kallikak/Euclidean/Euclid/sawtoothWave.h

const int16_t sawtoothWavetable[45][257] = {{-0,28031,27765,27259,27213,27036,26679,26531,26359,26050,25863,25691,25407,25200,25026,24759,24540,24363,24109,23881,23700,23457,23222,23038,22803,22565,22376,22149,21908,21714,21494,21252,21053,20838,20596,20392,20181,19940,19732,19524,19284,19072,18866,18629,18412,18208,17973,17753,17549,17318,17094,16890,16662,16435,16231,16006,15777,15572,15350,15120,14913,14694,14462,14254,14037,13805,13594,13380,13148,12935,12723,12492,12276,12065,11835,11617,11408,11179,10958,10749,10522,10299,10091,9866,9641,9433,9210,8983,8774,8553,8325,8115,7896,7668,7456,7240,7010,6797,6582,6353,6138,5925,5696,5479,5268,5040,4820,4610,4383,4162,3952,3726,3503,3294,3070,2845,2635,2413,2187,1976,1757,1529,1318,1100,872,659,443,214,-0,-214,-443,-659,-872,-1100,-1318,-1529,-1757,-1976,-2187,-2413,-2635,-2845,-3070,-3294,-3503,-3726,-3952,-4162,-4383,-4610,-4820,-5040,-5268,-5479,-5696,-5925,-6138,-6353,-6583,-6797,-7010,-7240,-7456,-7668,-7896,-8115,-8325,-8553,-8774,-8983,-9210,-9433,-9641,-9866,-10091,-10299,-10522,-10749,-10958,-11179,-11408,-11617,-11835,-12065,-12276,-12492,-12723,-12935,-13148,-13380,-13594,-13805,-14037,-14254,-14462,-14694,-14913,-15120,-15350,-15572,-15777,-16006,-16232,-16435,-16662,-16891,-17094,-17318,-17549,-17753,-17973,-18208,-18412,-18629,-18866,-19072,-19285,-19524,-19732,-19940,-20181,-20392,-20596,-20838,-21053,-21252,-21494,-21714,-21908,-22149,-22376,-22565,-22803,-23038,-23222,-23457,-23700,-23881,-24109,-24363,-24540,-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
};
