kallikak/Euclidean/Euclid/squareWave.h

const int16_t squareWavetable[45][257] = {{0,25902,25868,25602,25755,25802,25674,25732,25783,25701,25723,25773,25716,25718,25765,25726,25716,25759,25733,25716,25753,25738,25716,25748,25742,25718,25743,25745,25720,25739,25747,25722,25735,25748,25725,25732,25748,25728,25729,25748,25730,25727,25746,25733,25726,25745,25736,25725,25743,25739,25724,25741,25741,25725,25738,25743,25726,25736,25744,25727,25733,25745,25729,25731,25745,25731,25729,25745,25733,25727,25744,25736,25726,25743,25738,25725,25741,25741,25724,25739,25743,25725,25736,25745,25726,25733,25746,25727,25731,25748,25729,25727,25748,25732,25725,25748,25735,25722,25747,25739,25719,25745,25743,25718,25742,25748,25716,25738,25753,25716,25733,25759,25716,25726,25765,25719,25716,25773,25723,25701,25783,25732,25674,25802,25755,25602,25868,25902,-2,-25902,-25868,-25602,-25755,-25802,-25674,-25732,-25783,-25701,-25723,-25773,-25716,-25719,-25765,-25726,-25716,-25759,-25733,-25716,-25753,-25738,-25716,-25748,-25742,-25718,-25743,-25745,-25719,-25739,-25747,-25722,-25735,-25748,-25725,-25732,-25748,-25728,-25729,-25747,-25731,-25727,-25746,-25734,-25726,-25745,-25736,-25725,-25743,-25739,-25724,-25741,-25741,-25725,-25738,-25743,-25726,-25736,-25744,-25727,-25733,-25745,-25729,-25731,-25745,-25731,-25729,-25745,-25733,-25727,-25744,-25736,-25726,-25743,-25738,-25725,-25741,-25741,-25725,-25739,-25743,-25725,-25736,-25745,-25726,-25734,-25747,-25727,-25731,-25748,-25729,-25727,-25748,-25732,-25725,-25748,-25735,-25722,-25747,-257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
};
