kallikak/Euclidean/Euclid/triangleWave.h

const int16_t triangleWavetable[45][257] = {{0,-512,-1024,-1536,-2048,-2561,-3073,-3585,-4097,-4609,-5121,-5633,-6145,-6657,-7170,-7682,-8194,-8706,-9218,-9730,-10242,-10754,-11266,-11779,-12291,-12803,-13315,-13827,-14339,-14851,-15363,-15875,-16388,-16900,-17412,-17924,-18436,-18948,-19460,-19972,-20484,-20997,-21509,-22021,-22533,-23045,-23557,-24069,-24581,-25094,-25606,-26118,-26630,-27142,-27654,-28166,-28678,-29190,-29703,-30215,-30727,-31239,-31751,-32263,-32767,-32263,-31751,-31239,-30727,-30215,-29703,-29190,-28678,-28166,-27654,-27142,-26630,-26118,-25606,-25094,-24581,-24069,-23557,-23045,-22533,-22021,-21509,-20997,-20484,-19972,-19460,-18948,-18436,-17924,-17412,-16900,-16388,-15875,-15363,-14851,-14339,-13827,-13315,-12803,-12291,-11779,-11266,-10754,-10242,-9730,-9218,-8706,-8194,-7682,-7170,-6657,-6145,-5633,-5121,-4609,-4097,-3585,-3073,-2561,-2048,-1536,-1024,-512,0,512,1024,1536,2048,2561,3073,3585,4097,4609,5121,5633,6145,6657,7170,7682,8194,8706,9218,9730,10242,10754,11266,11779,12291,12803,13315,13827,14339,14851,15363,15875,16388,16900,17412,17924,18436,18948,19460,19972,20484,20997,21509,22021,22533,23045,23557,24069,24581,25094,25606,26118,26630,27142,27654,28166,28678,29190,29703,30215,30727,31239,31751,32263,32767,32263,31751,31239,30727,30215,29703,29190,28678,28166,27654,27142,26630,26118,25606,25094,24581,24069,23557,23045,22533,22021,21509,20997,20484,19972,19460,18948,18436,17924,17412,16900,16388,15875,15363,14851,14339,13827,13315,12803,1229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
};
