kallikak/Euclidean/Euclid/MIDIManager.h

#pragma once

#define MIDI_CLOCKS_PER_BEAT 12

typedef enum
{
  THIRD,
  HALF,
  UNITY,
  DOUBLE,
  TRIPLE
} ExtFactor;

void updateExtFactor(ExtFactor newFactor);

void managePlayState();

void setupMIDI();

void checkMIDI();

void resetMIDI();

void sendMIDINoteOn(byte note, byte vel, byte chan);

void sendMIDINoteOff(byte note, byte chan);

void stopAllMIDI();

void sendMIDIClock();

int getBPM();

void sendMIDIClockStart();

void sendMIDIClockContinue();

void sendMIDIClockStop();
