kallikak/Euclidean/Euclid/drum_samples.cpp

/*
  TODO:
    - Add the sample name to the config file
    - Deal better with missing/invalid data
 */

#include "stdlib.h"
#include "stdio.h"

#include "SD.h"
#include "Utility.h"

#include "drum_samples.h"

// default ids
#define DK_BASS       100
#define DK_SNARE      101
#define DK_HAT_C      102
#define DK_HAT_O      103
#define DK_TOM_L      104
#define DK_TOM_M      105
#define DK_TOM_H      106
#define DK_CLAVES			107
#define DK_CONGA_L		108
#define DK_CONGA_M		109
#define DK_CONGA_H    110
#define DK_CYMBAL     111
#define DK_RIDECYMBAL 112
#define DK_RIMSHOT    113
#define DK_MARACAS    114

#define NUM_DEFAULT_SAMPLES    15

// default kits
int numKits = 13;
drumKit *kits;
int numSamples = NUM_DEFAULT_SAMPLES;
int DK_LAST = DK_BASS + numSamples - 1;

#define NOSAMPLE (unsigned int *)0

unsigned int *drumSample1 = NOSAMPLE;
unsigned int *drumSample2 = NOSAMPLE;
unsigned int *drumSample3 = NOSAMPLE;
unsigned int *drumSample4 = NOSAMPLE;

bool isdefault[] = { true, true, true, true };

static char tempstr[50] = {0};
extern bool cardAvailable;

typedef char Str50[51];

Str50 *setNames;
int nSampleSets = 0;

int sampleSet = 0;

typedef struct {
  int id;
  char fname[51];
  char desc[16];
  char shortdesc[4];
} sampleinfo;

static sampleinfo *info = NULL;

bool makeDefaultKits()
{
  if (kits)
    free(kits);
  numKits = 13;
  kits = (drumKit *)calloc(numKits, sizeof(drumKit));
  if (!kits)
    return false;
  int k = 0;
  kits[k++] = {DK_BASS, DK_SNARE, DK_TOM_H, DK_HAT_C};
  kits[k++] = {DK_BASS, DK_SNARE, DK_HAT_O, DK_HAT_C}; 
  kits[k++] = {DK_BASS, DK_SNARE, DK_CYMBAL, DK_HAT_C}; 
  kits[k++] = {DK_BASS, DK_SNARE, DK_HAT_C, DK_RIDECYMBAL};  
  kits[k++] = {DK_BASS, DK_SNARE, DK_HAT_C, DK_HAT_O}; 
  kits[k++] = {DK_BASS, DK_SNARE, DK_SNARE, DK_HAT_C}; 
  kits[k++] = {DK_TOM_L, DK_TOM_M, DK_TOM_H, DK_HAT_C}; 
  kits[k++] = {DK_TOM_L, DK_TOM_M, DK_TOM_H, DK_CLAVES};
  kits[k++] = {DK_BASS, DK_BASS, DK_BASS, DK_HAT_O};
  kits[k++] = {DK_SNARE, DK_SNARE, DK_SNARE, DK_HAT_O};
  kits[k++] = {DK_SNARE, DK_SNARE, DK_RIMSHOT, DK_HAT_O};
  kits[k++] = {DK_CONGA_L, DK_CONGA_M, DK_CONGA_H, DK_HAT_C};
  kits[k++] = {DK_CONGA_L, DK_CONGA_M, DK_CONGA_H, DK_CLAVES};

  return true;
}

int getId(const char *name)
{
  for (int i = 0; i < numSamples; ++i)
    if (strcmp(info[i].fname, name) == 0)
      return DK_FIRST + i;
  return DK_OFF;
}

char *trim(char *str)
{
  char *end;

  // Trim leading space
  while(isspace((unsigned char)*str)) str++;

  if (*str == 0)  // All spaces?
    return str;

  // Trim trailing space
  end = str + strlen(str) - 1;
  while (end > str && isspace((unsigned char)*end)) 
    end--;

  // Write new null terminator character
  end[1] = '\0';

  return str;
}

bool parseDescription(char *setname, char *desc)
{
  int k = 0;
  while (*desc++ != ':')
  {
    if (!desc)
    {
      Serial.printf("Missing number of samples header in description file for sample set: %s\n", setname);
      return false;
    }
  }
  numSamples = (int)atol(desc);
  DBG(numSamples)
  DK_LAST = DK_BASS + numSamples - 1;
  desc = strchr(desc, '\n');

  if (info)
    free(info);
  info = (sampleinfo *)calloc(numSamples, sizeof(sampleinfo));
  if (!info)
    return false;
  
  bool loadinginfo = true;
  bool loadingkits = false;

  char *saveline;
  char *line = strtok_r(desc, "\n", &saveline);
  while (line)
  {
    if (line[0] == '#' || line[0] == '\n')
      continue;
    char *savetoken;
    char *token = strtok_r(line, ",", &savetoken);
    if (loadinginfo)
    {
      int n = strlen("Kits:");
      if (strncmp("Kits:", token, n) == 0)
      {
        loadingkits = true;
        loadinginfo = false;
        numKits = (int)atol(token + n);
        DBG(numKits)
        if (kits)
          free(kits);
        kits = (drumKit *)calloc(numKits, sizeof(drumKit));
        if (!kits)
        {
          Serial.printf("kit allocation failed\n");
          free(info);
          return false;
        }
        k = 0;
      }
      else
      {
        char *desc = strtok_r(NULL, ",", &savetoken);
        char *shortdesc = strtok_r(NULL, ",", &savetoken);
        sampleinfo entry = { DK_FIRST + k };
        if (!desc || !shortdesc)
        {
          Serial.printf("Invalid description file for sample set: %s\n", setname);
          return false;
        }
        strncpy(entry.fname, trim(token), 50);
        strncpy(entry.desc, trim(desc), 15);
        strncpy(entry.shortdesc, trim(shortdesc), 3);
        info[k++] = entry;
        DBGn(k)DBG(entry.fname)
      }
    }
    else if (loadingkits)
    {
      char *beat2 = strtok_r(NULL, ",", &savetoken);
      char *beat3 = strtok_r(NULL, ",", &savetoken);
      char *offbeat = strtok_r(NULL, ",", &savetoken);
      if (!beat2 || !beat3 || !offbeat)
      {
        Serial.printf("Improper kit definition in sample set: %s\n", setname);
        free(info);
        free(kits);
        return false;
      }
      kits[k].beats[0] = getId(trim(token));
      kits[k].beats[1] = getId(trim(beat2));
      kits[k].beats[2] = getId(trim(beat3));
      kits[k++].beats[3] = getId(trim(offbeat));
      DBG(k)
    }
    line = strtok_r(NULL, "\n", &saveline);
  }
  MSG("done")
  return true;
}

// char *defdesc =
//   "# Standard sample set description file\n"
//   "\n"
//   "Samples:15\n"
//   "\n"
//   "BASS,Bass,Bs\n"
//   "SNARE,Snare,Sn\n"
//   "HAT_C,Hi-hat,HH\n"
//   "HAT_O,Open Hi-hat,OH\n"
//   "TOM_L,Low Tom,LT\n"
//   "TOM_M,Med Tom,MT\n"
//   "TOM_H,High Tom,HT\n"
//   "CLAVES,Claves,Clv\n"
//   "CONGA_L,Low Conga,LC\n"
//   "CONGA_M,Med Conga,MC\n"
//   "CONGA_H,High Conga,HC\n"
//   "CYMBAL,Cymbal,Cy\n"
//   "RIDE,Ride Cymbal,Rd\n"
//   "RIM,Rimshot,Rim\n"
//   "MARACAS,Maracas,Mar\n"
//   "\n"
//   "Kits:13\n"
//   "\n"
//   "BASS,SNARE,TOM_H,HAT_C\n"
//   "BASS,SNARE,HAT_O,HAT_C\n"
//   "BASS,SNARE,CYMBAL,HAT_C \n"
//   "BASS,SNARE,HAT_C,RIDE\n"
//   "BASS,SNARE,HAT_C,HAT_O\n"
//   "BASS,SNARE,SNARE,HAT_C \n"
//   "TOM_L,TOM_M,TOM_H,HAT_C \n"
//   "TOM_L,TOM_M,TOM_H,CLAVES\n"
//   "BASS,BASS,BASS,HAT_O\n"
//   "SNARE,SNARE,SNARE,HAT_O\n"
//   "SNARE,SNARE,RIM,HAT_O\n"
//   "CONGA_L,CONGA_M,CONGA_H,HAT_C\n"
//   "CONGA_L,CONGA_M,CONGA_H,CLAVES\n";

bool loadSampleDesc(int sampleSet)
{
  if (sampleSet < 0 || sampleSet >= nSampleSets)
  {
    if (!makeDefaultKits())
      return false;
    if (info)
    {
      free(info);
      info = NULL;
    }

    numSamples = NUM_DEFAULT_SAMPLES;
    DK_LAST = DK_BASS + numSamples - 1;

    return true;
  }

  char *setname = setNames[sampleSet];

  sprintf(tempstr, "/Samples/%s", setname);
  if (!SD.exists(tempstr))
  {
    Serial.print("No description file for sample set: ");
    Serial.println(setname);
    return false;
  }
  sprintf(tempstr, "/Samples/%s/desc.txt", setname);  
  File sampledesc = SD.open(tempstr, FILE_READ);

  char *desc = (char *)calloc(sampledesc.size() + 1, sizeof(char));
  if (!desc)
    return false;
  char *save = desc;

  while (sampledesc.available())
    *desc++ = sampledesc.read();

  MSG("Loaded sample description")
  
  bool result = parseDescription(setname, save);
  free(save);

  return result;
}

const char *getInstrumentDesc(int type, bool shortDesc)
{
  if (info)
  {
    if (type < DK_FIRST || type > DK_LAST)
      return "None";
    int k = type - DK_FIRST;
    return shortDesc ? info[k].shortdesc : info[k].desc;
  }
  else
  {
    switch (type)
    {
      case DK_BASS:
        return shortDesc ? "Bs" : "Bass";
      case DK_CLAVES:
        return shortDesc ? "Clv" : "Claves";
      case DK_CONGA_H:
        return shortDesc ? "HC" : "High Conga";
      case DK_CONGA_L:
        return shortDesc ? "LC" : "Low Conga";
      case DK_CONGA_M:
        return shortDesc ? "MC" : "Med Conga";
      case DK_CYMBAL:
        return shortDesc ? "Cy" : "Cymbal";
      case DK_HAT_C:
        return shortDesc ? "HH" : "Hi-hat";
      case DK_HAT_O:
        return shortDesc ? "OH" : "Open Hi-hat";
      case DK_MARACAS:
        return shortDesc ? "Mar" : "Maracas";
      case DK_RIDECYMBAL:
        return shortDesc ? "Rd" : "Ride Cymbal";
      case DK_RIMSHOT:
        return shortDesc ? "Rim" : "Rimshot";
      case DK_SNARE:
        return shortDesc ? "Sn" : "Snare";
      case DK_TOM_H:
        return shortDesc ? "HT" : "High Tom";
      case DK_TOM_L:
        return shortDesc ? "LT" : "Low Tom";
      case DK_TOM_M:
        return shortDesc ? "MT" : "Med Tom";
      default:
        return "None";
    }
  }
}

int getNumSampleSets()
{
  return nSampleSets;
}

char *getSetName(int k)
{
  if (k < 0 || k >= nSampleSets)
    return (char *)"Default";
  if (k < nSampleSets)
    return setNames[k];
  else
    return (char *)"";
}

void loadSampleSet(char *samplesetname)
{
  int k = -1;
  bool found = false;
  while (k < nSampleSets)
  {
    if (strncmp(samplesetname, getSetName(k), MAX_SAMPLESET_NAME_LENGTH) == 0)
    {
      sampleSet = k;
      loadSampleDesc(sampleSet);
      found = true;
      break;
    }
    k++;
  }
  if (!found)
    loadSampleDesc(-1); // defaults

  needsKitUpdate = true;
}

void initSamples()
{
  if (cardAvailable)
  {
    File sampleFolder = SD.open("/Samples");
    nSampleSets = 0;
    while (true)
    {
      File set =  sampleFolder.openNextFile();
      if (!set)
        break;
      if (set.isDirectory())
      {
        const char *name = set.name();
        sprintf(tempstr, "/Samples/%s/desc.txt", name);
        if (SD.exists(tempstr))
          nSampleSets++;
      }
    }
    setNames = (Str50 *)calloc(nSampleSets, sizeof(Str50));
    unsigned int k = 0;
    sampleFolder = SD.open("/Samples");
    while (true)
    {
      File set =  sampleFolder.openNextFile();
      if (!set)
        break;
      if (set.isDirectory())
      {
        const char *name = set.name();
        sprintf(tempstr, "/Samples/%s/desc.txt", name);
        if (SD.exists(tempstr))
        {
          Serial.println(name);
          if (strlen(name) <= 50)
            strcpy(setNames[k++], name);
        }
      }
    }
  }
  sampleSet = -1; // indicates inbuilt default samples
  makeDefaultKits();
}

const unsigned int *getDefaultSample(int sample)
{
  switch (sample)
  {
    case DK_BASS: return DK_BASS_ARRAY;
    case DK_HAT_C: return DK_HAT_C_ARRAY;
    case DK_HAT_O: return DK_HAT_O_ARRAY;
    case DK_SNARE: return DK_SNARE_ARRAY;
    case DK_TOM_L: return DK_TOM_L_ARRAY;
    case DK_TOM_M: return DK_TOM_M_ARRAY;
    case DK_TOM_H: return DK_TOM_H_ARRAY;
    case DK_CLAVES: return DK_CLAVES_ARRAY;
    case DK_CONGA_H: return DK_CONGA_H_ARRAY;
    case DK_CONGA_L: return DK_CONGA_L_ARRAY;
    case DK_CONGA_M: return DK_CONGA_M_ARRAY;
    case DK_CYMBAL: return DK_CYMBAL_ARRAY;
    case DK_MARACAS: return DK_MARACAS_ARRAY;
    case DK_RIMSHOT: return DK_RIMSHOT_ARRAY;
    case DK_RIDECYMBAL: return DK_RIDECYMBAL_ARRAY;
    case DK_OFF:
    default:
      return NOSAMPLE;
  }
}

#define BR_44K 0x83
#define BR_22K 0x82
#define BR_11K 0x81
unsigned int *getSample(int s, unsigned int *buffer, int bufidx)
{
  if (s < DK_FIRST || s > DK_LAST)
    return NOSAMPLE;

  if (!cardAvailable || sampleSet < 0 || sampleSet >= nSampleSets)
  {
    isdefault[bufidx] = true;
    return (unsigned int *)getDefaultSample(s);
  }

  const char *samplename = info[s - DK_FIRST].fname;
  unsigned char rawformat = 0;

  sprintf(tempstr, "/Samples/%s/%s.ulw", getSetName(sampleSet), samplename);
  if (SD.exists(tempstr))
    goto found;
  sprintf(tempstr, "/Samples/%s/%s.r11", getSetName(sampleSet), samplename);
  if (SD.exists(tempstr))
  {
    rawformat = BR_11K;
    goto found;
  }
  sprintf(tempstr, "/Samples/%s/%s.r22", getSetName(sampleSet), samplename);
  if (SD.exists(tempstr))
  {
    rawformat = BR_22K;
    goto found;
  }
  sprintf(tempstr, "/Samples/%s/%s.r44", getSetName(sampleSet), samplename);
  if (SD.exists(tempstr))
  {
    rawformat = BR_44K;
    goto found;
  }
  sprintf(tempstr, "/Samples/%s/%s.raw", getSetName(sampleSet), samplename);
  if (SD.exists(tempstr))
  {
    rawformat = BR_44K;
    goto found;
  }
  return NOSAMPLE;

found:
  File sample = SD.open(tempstr, FILE_READ);

  size_t nbytes = sample.size();
  if (!isdefault[bufidx] && buffer)
    free(buffer);
  isdefault[bufidx] = false;    
  buffer = (unsigned int *)calloc(nbytes + 4, sizeof(byte));
  if (buffer)
  {
    sample.read(rawformat ? &buffer[1] : buffer, nbytes);
    if (rawformat)
    {
      uint32_t header = (rawformat << 24) + nbytes; // patch in the header
      buffer[0] = header;
    }
  }
  sample.close();
  return buffer;
}

void updateSamples(int s1, int s2, int s3, int s4)
{
  if (s1 != DK_OFF)
  {
    drumSample1 = getSample(s1, drumSample1, 0);
    if (drumSample1 == NOSAMPLE) Serial.printf("Failed to load %d [%s]\n", s1, info[s1 - DK_FIRST].fname);
  }
  if (s2 != DK_OFF) 
  {
    drumSample2 = getSample(s2, drumSample2, 1); 
    if (drumSample2 == NOSAMPLE) Serial.printf("Failed to load %d [%s]\n", s2, info[s2 - DK_FIRST].fname);
  }
  if (s3 != DK_OFF)
  {
    drumSample3 = getSample(s3, drumSample3, 2); 
    if (drumSample3 == NOSAMPLE) Serial.printf("Failed to load %d [%s]\n", s3, info[s3 - DK_FIRST].fname);
  }
  if (s4 != DK_OFF)
  {
    drumSample4 = getSample(s4, drumSample4, 3); 
    if (drumSample4 == NOSAMPLE) Serial.printf("Failed to load %d [%s]\n", s4, info[s4 - DK_FIRST].fname);
  }
}

// Converted from 01-BassDrum.wav, using 44100 Hz, u-law encoding
const unsigned int AudioSampleBassdrum[1249] = {
0x01001337,0x06060606,0x29800606,0x4E4E4E48,0x46494D4E,0x31373E42,0x9E911425,0xB1AEA9A5,
0xB9B7B5B3,0xBFBDBCBA,0xC1C1C0C0,0xC1C1C1C1,0x22B5BFC0,0x4B49453F,0x4F4E4E4C,0x50505050,
0x50505050,0x51515151,0x51515151,0x51515151,0x52525252,0x51515151,0x50505051,0x4F4F5050,
0x4D4D4E4E,0x4A4B4C4C,0x4848494A,0x45464647,0x42434344,0x3D3F4041,0x3637393B,0x2C303233,
0x19202428,0x978D0210,0xABA7A39E,0xB5B3B1AF,0xBAB9B8B6,0xBCBCBCBB,0xB9BBBBBC,0xAFB3B5B8,
0x0894A2AA,0x3631291F,0x4643403C,0x504E4B48,0x55545251,0x59585756,0x5D5C5B5A,0x605F5F5E,
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
0x5A5A5A5A,0x5A5A5A5A,0x5A5A5A5A,0x595A5A5A,0x59595959,0x59595959,0x59595959,0x59595959,
0x59595959,0x58585858,0x58585858,0x58585858,0x57575758,0x57575757,0x56565657,0x55565656,
0x53545455,0x51525253,0x4E505051,0x4A4B4C4D,0x46474849,0x41424345,0x3B3D3F40,0x32343739,
0x24282D30,0x80101820,0xA4A09890,0xB2B0ACA8,0xBAB8B6B4,0xC1C0BEBC,0xC5C4C3C2,0xC9C8C7C6,
0xCDCCCBCA,0xD0D0CFCE,0xD2D1D1D1,0xD4D3D3D2,0xD5D5D4D4,0xD7D6D6D6,0xD8D7D7D7,0xD9D8D8D8,
0xDAD9D9D9,0xDADADADA,0xDBDBDBDA,0xDBDBDBDB,0xDCDCDBDB,0xDCDCDCDC,0xDCDCDCDC,0xDBDBDCDC,
0xDBDBDBDB,0xDBDBDBDB,0xDADADADB,0xDADADADA,0xD9D9D9D9,0xD8D8D8D9,0xD7D7D7D8,0xD6D6D6D7,
0xD4D5D5D5,0xD3D3D3D4,0xD1D1D2D2,0xCFD0D0D1,0xCBCCCDCE,0xC8C8C9CA,0xC4C5C6C7,0xC0C1C2C3,
0xB7B9BCBE,0xAEB1B3B5,0x9CA2A6AA,0x15098794,0x2A26221D,0x3533312F,0x3D3B3937,0x4241403F,
0x46454443,0x4B4A4948,0x4E4D4D4C,0x5150504F,0x52525251,0x54545353,0x55555554,0x57565656,
0x58575757,0x58585858,0x59595858,0x59595959,0x59595959,0x59595959,0x59595959,0x59595959,
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
};
